kakaroto/RAMBO-Test-Jig/stl/RAMBo_1.1/RAMBo_bottom_plate.stl

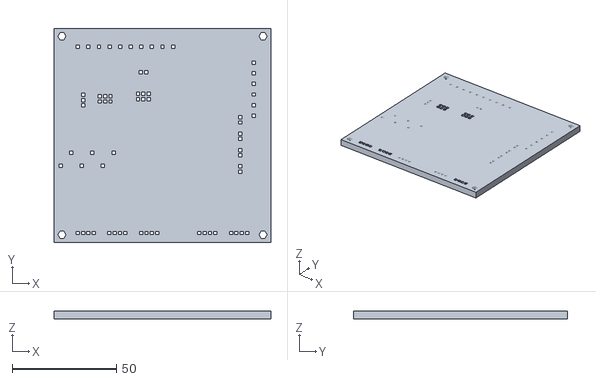
[picture p15: CAD file, 2013-11-21]
stl/RAMBo_1.1/RAMBo_bottom_plate.stl
104.1 x 102.9 x 4.00
