kakaroto/RAMBO-Test-Jig/stl/RAMBo_1.3/RAMBo_bottom_plate.stl

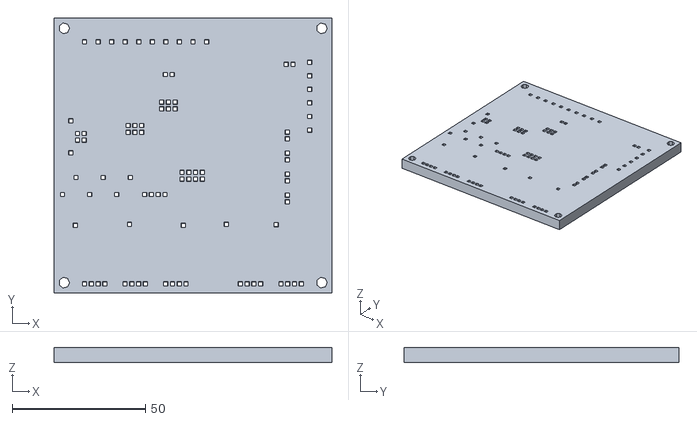
[picture p16: CAD file, 2014-11-15]
stl/RAMBo_1.3/RAMBo_bottom_plate.stl
104.1 x 102.9 x 5.50
