kakaroto/RAMBO-Test-Jig/stl/RAMBo_1.1/RAMBo_middle_plate.stl

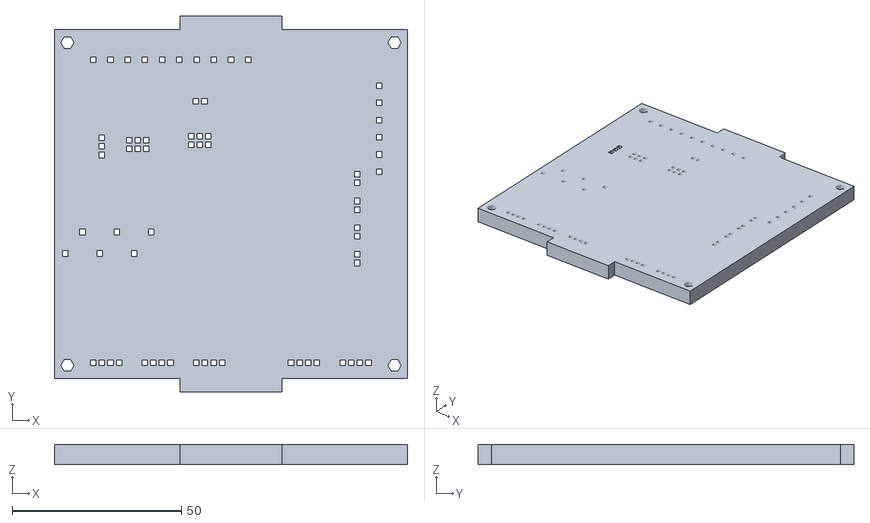
[picture p17: CAD file, 2013-11-21]
stl/RAMBo_1.1/RAMBo_middle_plate.stl
104.1 x 110.9 x 6.00
