kakaroto/RAMBO-Test-Jig/stl/RAMBo_1.3/clamp.stl

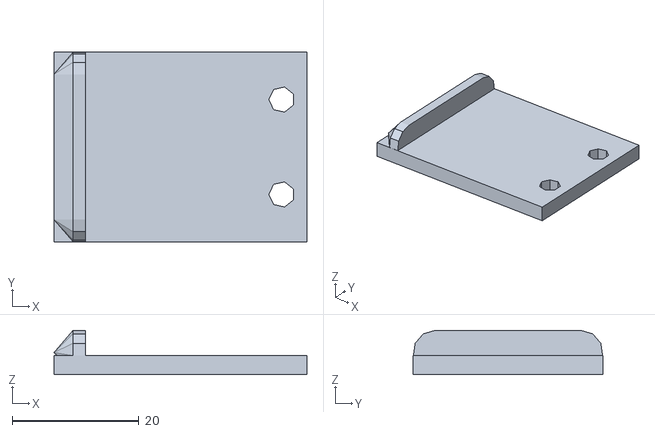
[picture p18: CAD file, 2014-11-15]
stl/RAMBo_1.3/clamp.stl
40.0 x 30.0 x 7.00
