kakaroto/RAMBO-Test-Jig/bottom_spacer.scad

include <common.scad>;

spacer(BOTTOM_SPACER_HEIGHT);
