kakaroto/RAMBO-Test-Jig/RAMBo_bottom_plate.scad

include <common.scad>;

color("green") RAMBo(1.0, 1.5); //Show bottom
    
translate([0, 0, 1.0])
      RAMBo(4.5, 1.65); //Show top module
